tomapel721/Telemetry-Transmitter/Transmitter/SourceCode/Core/Src/NRF24/nRF24.c

/*
 * nRF24.c
 *
 *  Created on: Apr 26, 2020
 *      Author: Mateusz Salamon
 */

#include "main.h"
#include "spi.h"

#include "nRF24/nRF24.h"
#include "nRF24/nRF24_Defs.h"
#include "NRF24/ring_buffer.h"


static SPI_HandleTypeDef *hspi_nrf;

static uint8_t addr_p0_backup[NRF24_ADDR_SIZE];

#if (NRF24_USE_INTERRUPT == 1)
static uint8_t nrf24_rx_flag, nrf24_tx_flag, nrf24_mr_flag;
static volatile uint8_t Nrf24InterruptFlag, Nrf24RXReadyDataFlag;
#endif

#if (NRF24_USE_INTERRUPT == 1)
#if (NRF24_USE_RINGBUFFER == 1)
static uint8_t Nrf24TXFreeFlag;
static RingBuffer *RXBuffer, *TXBuffer;
#endif
#if (NRF24_USE_RINGBUFFER == 0)
static uint8_t RXBuffer[32];
static uint8_t RXDataCounter;
#endif
#endif

//
// BASIC READ/WRITE FUNCTIONS
//
// Define these function for your MCU
//

#define NRF24_CSN_HIGH		HAL_GPIO_WritePin(NRF24_CSN_GPIO_Port, NRF24_CSN_Pin, GPIO_PIN_SET)
#define NRF24_CSN_LOW		HAL_GPIO_WritePin(NRF24_CSN_GPIO_Port, NRF24_CSN_Pin, GPIO_PIN_RESET)

#define NRF24_CE_HIGH		HAL_GPIO_WritePin(NRF24_CE_GPIO_Port, NRF24_CE_Pin, GPIO_PIN_SET)
#define NRF24_CE_LOW		HAL_GPIO_WritePin(NRF24_CE_GPIO_Port, NRF24_CE_Pin, GPIO_PIN_RESET)

static void nRF24_Delay_ms(uint8_t Time)
{
	HAL_Delay(Time);
}

static void nRF24_SendSpi(uint8_t *Data, uint8_t Length)
{
	HAL_SPI_Transmit(hspi_nrf, Data, Length, 1000);
}

static void nRF24_ReadSpi(uint8_t *Data, uint8_t Length)
{
	HAL_SPI_Receive(hspi_nrf, Data, Length, 1000);
}

//
// END OF BASIC READ/WRITE FUNCTIONS
//
static uint8_t nRF24_ReadRegister(uint8_t reg)
{
	uint8_t result;

	reg = NRF24_CMD_R_REGISTER | reg;

	NRF24_CSN_LOW;
	nRF24_SendSpi(&reg, 1);
	nRF24_ReadSpi(&result, 1);
	NRF24_CSN_HIGH;

	return result;
}

static void nRF24_ReadRegisters(uint8_t reg, uint8_t* ret, uint8_t len)
{
	reg = NRF24_CMD_R_REGISTER | reg;

	NRF24_CSN_LOW;

	nRF24_SendSpi(&reg, 1);
	nRF24_ReadSpi(ret, len);

	NRF24_CSN_HIGH;
}

static void nRF24_WriteRegister(uint8_t reg, uint8_t val)
{
	uint8_t tmp[2];

	tmp[0] = NRF24_CMD_W_REGISTER | reg;
	tmp[1] = val;

	NRF24_CSN_LOW;

	nRF24_SendSpi(tmp, 2);

	NRF24_CSN_HIGH;
}

static void nRF24_WriteRegisters(uint8_t reg, uint8_t* val, uint8_t len)
{
	reg = NRF24_CMD_W_REGISTER | reg;

	NRF24_CSN_LOW;

	nRF24_SendSpi(&reg, 1);
	nRF24_SendSpi(val, len);

	NRF24_CSN_HIGH;
}

void nRF24_RX_Mode(void)
{
	uint8_t config = nRF24_ReadConfig();
	// Restore pipe 0 adress after comeback from TX mode
	nRF24_SetRXAddress(0, addr_p0_backup);
	// PWR_UP bit set
	config |= (1<<NRF24_PWR_UP);
	// PRIM_RX bit set
	config |= (1<<NRF24_PRIM_RX);
	nRF24_WriteConfig(config);
	// Reset status
	nRF24_WriteStatus((1<<NRF24_RX_DR)|(1<<NRF24_TX_DS)|(1<<NRF24_MAX_RT));
	// Flush RX
	nRF24_FlushRX();
	// Flush TX
	nRF24_FlushTX();

	NRF24_CE_HIGH;
	nRF24_Delay_ms(1);
}

void nRF24_TX_Mode(void)
{
	NRF24_CE_LOW;

	uint8_t config = nRF24_ReadConfig();
	// PWR_UP bit set
	config |= (1<<NRF24_PWR_UP);
	// PRIM_RX bit low
	config &= ~(1<<NRF24_PRIM_RX);
	nRF24_WriteConfig(config);
	// Reset status
	nRF24_WriteStatus((1<<NRF24_RX_DR)|(1<<NRF24_TX_DS)|(1<<NRF24_MAX_RT));
	// Flush RX
	nRF24_FlushRX();
	// Flush TX
	nRF24_FlushTX();

	nRF24_Delay_ms(1);
}

uint8_t nRF24_ReadConfig(void)
{
	return (nRF24_ReadRegister(NRF24_CONFIG));
}

void nRF24_WriteConfig(uint8_t conf)
{
	nRF24_WriteRegister(NRF24_CONFIG, conf);
}

void nRF24_SetPALevel(uint8_t lev)
{
	uint8_t rf_setup = nRF24_ReadRegister(NRF24_RF_SETUP);
	rf_setup &= 0xF8; // Clear PWR bits
	rf_setup |= (lev<<1);
	nRF24_WriteRegister(NRF24_RF_SETUP, rf_setup);
}

void nRF24_SetDataRate(uint8_t dr)
{
	uint8_t rf_setup = nRF24_ReadRegister(NRF24_RF_SETUP);
	rf_setup &= 0xD7; // Clear DR bits (1MBPS)
	if(dr == NRF24_RF_DR_250KBPS)
		rf_setup |= (1<<NRF24_RF_DR_LOW);
	else if(dr == NRF24_RF_DR_2MBPS)
		rf_setup |= (1<<NRF24_RF_DR_HIGH);
	nRF24_WriteRegister(NRF24_RF_SETUP, rf_setup);
}

uint8_t nRF24_ReadStatus(void)
{
	return (nRF24_ReadRegister(NRF24_STATUS));
}

void nRF24_WriteStatus(uint8_t st)
{
	nRF24_WriteRegister(NRF24_STATUS, st);
}

//
// FIFO Status
//

uint8_t nRF24_ReadFifoStatus(void)
{
	return (nRF24_ReadRegister(NRF24_FIFO_STATUS));
}

void nRF24_WriteFifoStatus(uint8_t st)
{
	nRF24_WriteRegister(NRF24_FIFO_STATUS, st);
}

uint8_t nRF24_IsBitSetInFifoStatus(uint8_t Bit)
{
	uint8_t FifoStatus;

	FifoStatus = nRF24_ReadFifoStatus();

	if(FifoStatus & (1<<Bit))
	{
		return 1;
	}

	return 0;
}

uint8_t nRF24_IsTxReuse(void)
{
	return nRF24_IsBitSetInFifoStatus(NRF24_TX_REUSE);
}

uint8_t nRF24_IsTxFull(void)
{
	return nRF24_IsBitSetInFifoStatus(NRF24_TX_FULL);
}

uint8_t nRF24_IsTxEmpty(void)
{
	return nRF24_IsBitSetInFifoStatus(NRF24_TX_EMPTY);
}

uint8_t nRF24_IsRxFull(void)
{
	return nRF24_IsBitSetInFifoStatus(NRF24_RX_FULL);
}

uint8_t nRF24_IsRxEmpty(void)
{
	return nRF24_IsBitSetInFifoStatus(NRF24_RX_EMPTY);
}

void nRF24_FlushRX(void)
{
	uint8_t command = NRF24_CMD_FLUSH_RX;

	NRF24_CSN_LOW;
	nRF24_SendSpi(&command, 1);
	NRF24_CSN_HIGH;
}

void nRF24_FlushTX(void)
{
	uint8_t command = NRF24_CMD_FLUSH_TX;

	NRF24_CSN_LOW;
	nRF24_SendSpi(&command, 1);
	NRF24_CSN_HIGH;
}

void nRF24_EnableCRC(uint8_t onoff)
{
	uint8_t config = nRF24_ReadConfig();

	if(onoff)
		config |= (1<<NRF24_EN_CRC);
	else
		config &= ~(1<<NRF24_EN_CRC);
	nRF24_WriteConfig(config);
}

void nRF24_SetCRCLength(uint8_t crcl)
{
	uint8_t config = nRF24_ReadConfig();
	if(crcl == NRF24_CRC_WIDTH_2B)
		config |= (1<<NRF24_CRCO);
	else
		config &= ~(1<<NRF24_CRCO);
	nRF24_WriteConfig(config);
}

void nRF24_SetRetries(uint8_t ard, uint8_t arc)
{
	// ard * 250us, arc repeats
	nRF24_WriteRegister(NRF24_SETUP_RETR, (((ard & 0x0F)<<NRF24_ARD) | ((arc & 0x0F)<<NRF24_ARC)));
}

void nRF24_SetRFChannel(uint8_t channel)
{
	nRF24_WriteRegister(NRF24_RF_CH, (channel & 0x7F));
}

void nRF24_SetPayloadSize(uint8_t pipe, uint8_t size)
{
	if(pipe > 5)
		pipe = 5; // Block too high pipe number
	nRF24_WriteRegister(NRF24_RX_PW_P0 + pipe , (size & 0x3F));
}

void nRF24_EnablePipe(uint8_t pipe, uint8_t onoff)
{
	if(pipe > 5)
		pipe = 5; // Block too high pipe number
	uint8_t enable_pipe = nRF24_ReadRegister(NRF24_EN_RXADDR);
	if(onoff == 1)
		enable_pipe |= (1<<pipe);
	else
		enable_pipe &= ~(1<<pipe);
	nRF24_WriteRegister(NRF24_EN_RXADDR, enable_pipe);
}

void nRF24_AutoACK(uint8_t pipe, uint8_t onoff)
{
	if(pipe > 5)
		pipe = 5; // Block too high pipe number
	uint8_t enaa = nRF24_ReadRegister(NRF24_EN_AA);
	if(onoff == 1)
		enaa |= (1<<pipe);
	else
		enaa &= ~(1<<pipe);
	nRF24_WriteRegister(NRF24_EN_AA, enaa);
}

void nRF24_SetAddressWidth(uint8_t size)
{
	if(size > 5)
		size = 5; // Maximum are 5 bytes
	if(size < 3)
		size = 3; // Minimum are 3 bytes
	nRF24_WriteRegister(NRF24_SETUP_AW, ((size-2) & 0x03));
}

void nRF24_SetRXAddress(uint8_t pipe, const uint8_t* address)
{
	// pipe 0 and pipe 1 are fully 40-bits storaged
	// pipe 2-5 is storaged only with last byte. Rest are as same as pipe 1
	// pipe 0 and 1 are LSByte first so they are needed to reverse address
	if((pipe == 0) || (pipe == 1))
	{
		uint8_t i;
		uint8_t address_rev[NRF24_ADDR_SIZE];
		for(i = 0; i<NRF24_ADDR_SIZE; i++)
			address_rev[NRF24_ADDR_SIZE - 1 - i] = address[i];
		nRF24_WriteRegisters(NRF24_RX_ADDR_P0 + pipe, address_rev, NRF24_ADDR_SIZE);
	}
	else
		nRF24_WriteRegister(NRF24_RX_ADDR_P0 + pipe, address[NRF24_ADDR_SIZE-1]);
}

void nRF24_SetTXAddress(const uint8_t* address)
{
	// TX address is storaged similar to RX pipe 0 - LSByte first
	uint8_t i;
	uint8_t address_rev[NRF24_ADDR_SIZE];

	nRF24_ReadRegisters(NRF24_RX_ADDR_P0, address_rev, NRF24_ADDR_SIZE); // Backup P0 address
	for(i = 0; i<NRF24_ADDR_SIZE; i++)
		addr_p0_backup[NRF24_ADDR_SIZE - 1 - i] = address_rev[i]; //Reverse P0 address

	for(i = 0; i<NRF24_ADDR_SIZE; i++)
		address_rev[NRF24_ADDR_SIZE - 1 - i] = address[i];
	//make pipe 0 address backup;

	nRF24_WriteRegisters(NRF24_RX_ADDR_P0, address_rev, NRF24_ADDR_SIZE); // Pipe 0 must be same for auto ACk
	nRF24_WriteRegisters(NRF24_TX_ADDR, address_rev, NRF24_ADDR_SIZE);
}

void nRF24_ClearInterrupts(void)
{
	uint8_t status = nRF24_ReadStatus();
	status |= (7<<4); // Clear bits 4, 5, 6.
	nRF24_WriteStatus(status);
}

uint8_t nRF24_GetDynamicPayloadSize(void)
{
    uint8_t result = 0;

    result = nRF24_ReadRegister(NRF24_CMD_R_RX_PL_WID);

    if (result > 32) // Something went wrong :)
    {
        nRF24_FlushRX();
        nRF24_Delay_ms(2);
        return 0;
    }
    return result;
}

void nRF24_EnableRXDataReadyIRQ(uint8_t onoff)
{
	uint8_t config = nRF24_ReadConfig();

	if(!onoff)
		config |= (1<<NRF24_RX_DR);
	else
		config &= ~(1<<NRF24_RX_DR);

	nRF24_WriteConfig(config);
}

void nRF24_EnableTXDataSentIRQ(uint8_t onoff)
{
	uint8_t config = nRF24_ReadConfig();

	if(!onoff)
		config |= (1<<NRF24_TX_DS);
	else
		config &= ~(1<<NRF24_TX_DS);

	nRF24_WriteConfig(config);
}

void nRF24_EnableMaxRetransmitIRQ(uint8_t onoff)
{
	uint8_t config = nRF24_ReadConfig();

	if(!onoff)
		config |= (1<<NRF24_MAX_RT);
	else
		config &= ~(1<<NRF24_MAX_RT);

	nRF24_WriteConfig(config);
}

void nRF24_WriteTXPayload(uint8_t * data, __attribute__((unused))uint8_t size)
{
#if (NRF24_DYNAMIC_PAYLOAD == 1)
	nRF24_WriteRegisters(NRF24_CMD_W_TX_PAYLOAD, data, size);
#else
	nRF24_WriteRegisters(NRF24_CMD_W_TX_PAYLOAD, data, NRF24_PAYLOAD_SIZE);
#endif
}

void nRF24_WaitTX()
{
	uint8_t status;
	NRF24_CE_HIGH;
	nRF24_Delay_ms(1);
	NRF24_CE_LOW;
	do
	{
		nRF24_Delay_ms(1);
		status = nRF24_ReadStatus();
	}while(!((status & (1<<NRF24_MAX_RT)) || (status & (1<<NRF24_TX_DS))));
}

void nRF24_ReadRXPaylaod(uint8_t *data, __attribute__((unused))uint8_t *size)
{
#if (NRF24_DYNAMIC_PAYLOAD == 1)
	*size = nRF24_GetDynamicPayloadSize();
	nRF24_ReadRegisters(NRF24_CMD_R_RX_PAYLOAD, data, *size);
#else
	nRF24_ReadRegisters(NRF24_CMD_R_RX_PAYLOAD, data, NRF24_PAYLOAD_SIZE);
#endif
#if (NRF24_INTERRUPT_MODE == 0)
	nRF24_WriteRegister(NRF24_STATUS, (1<NRF24_RX_DR));
	if(nRF24_ReadStatus() & (1<<NRF24_TX_DS))
		nRF24_WriteRegister(NRF24_STATUS, (1<<NRF24_TX_DS));
#endif
}

nRF24_TX_Status nRF24_SendPacket(uint8_t* Data, uint8_t Size)
{
	if(Size > 32)
		return NRF24_NO_TRANSMITTED_PACKET;

	nRF24_WriteTXPayload(Data, Size);
#if (NRF24_USE_RINGBUFFER == 0)
	nRF24_WaitTX();
#endif


	return NRF24_TRANSMITTED_PACKET;
}

#if (NRF24_USE_RINGBUFFER == 1)
uint8_t nRF24_IsSomtehingToRead(void)
{
	return RB_ElementsAvailable(RXBuffer)?1:0;
}

uint8_t nRF24_IsSomtehingToSend(void)
{
	return RB_ElementsAvailable(TXBuffer)?1:0;
}
#endif

uint8_t nRF24_RXAvailable(void)
{
#if (NRF24_USE_INTERRUPT == 0)
	uint8_t status = nRF24_ReadStatus();

	// RX FIFO Interrupt
	if ((status & (1 << 6)))
	{
		status |= (1<<6); // Interrupt flag clear
		nRF24_WriteStatus(status);
		return 1;
	}
	return 0;
#endif
#if (NRF24_USE_INTERRUPT == 1) && (NRF24_USE_RINGBUFFER == 0)
	if(RXDataCounter > 0)
	{
		return 1;
	}
	return 0;
#endif
#if (NRF24_USE_RINGBUFFER == 1)
	return nRF24_IsSomtehingToRead();
#endif
}

nRF24_RX_Status nRF24_ReceivePacket(uint8_t* Data, uint8_t *Size)
{
#if (NRF24_USE_INTERRUPT == 0)
	if(nRF24_RXAvailable())
	{
#endif
		nRF24_ReadRXPaylaod(Data, Size);
		return NRF24_RECEIVED_PACKET;
#if (NRF24_USE_INTERRUPT == 0)
	}
	return NRF24_NO_RECEIVED_PACKET;
#endif

}

nRF24_TX_Status nRF24_SendData(uint8_t* Data, uint8_t Size)
{
static int licznikRamek = 0;
#if (NRF24_USE_RINGBUFFER != 1) // (NRF24_USE_INTERRUPT any)
	return nRF24_SendPacket(Data, Size);
#endif
#if (NRF24_USE_RINGBUFFER == 1)
	uint8_t i = 0;

	while(Size > 0)
	{
		if(RB_OK == RB_WriteToBuffer(TXBuffer, Data[i++]))
		{
			Size--;
		}
		else
		{
			return NRF24_NO_TRANSMITTED_PACKET;
		}
	}
	licznikRamek++;
	return NRF24_TRANSMITTED_PACKET;
#endif
}
#if (NRF24_USE_RINGBUFFER == 1)
void nRF24_CheckTXAndSend(void)
{
	uint8_t i, DataCounter;
	uint8_t TXPacket[32];

	if(nRF24_IsSomtehingToSend() && Nrf24TXFreeFlag)
	{
		nRF24_TX_Mode();

		Nrf24TXFreeFlag = 0;
		DataCounter = RB_ElementsAvailable(TXBuffer);
		if(DataCounter > 32)
		{
			DataCounter = 32; // Max Payload
		}

		for(i = 0; i < DataCounter; i++)
		{
			RB_ReadFromBuffer(TXBuffer, &TXPacket[i]);
		}

		nRF24_SendPacket(TXPacket, DataCounter);
		NRF24_CE_HIGH;
		nRF24_Delay_ms(1);
		NRF24_CE_LOW;
	}
}
#endif
#if (NRF24_USE_INTERRUPT == 1)
void nRF24_ReceiveData(void)
{
#if (NRF24_USE_RINGBUFFER == 1)
	uint8_t i, DataCounter;
	uint8_t RXPacket[32];
	do
	{
		nRF24_ReceivePacket(RXPacket, &DataCounter);

		for(i = 0; i < DataCounter; i++)
		{
			RB_WriteToBuffer(RXBuffer, RXPacket[i]);
		}

	}while(!nRF24_IsRxEmpty());
#endif
#if (NRF24_USE_RINGBUFFER == 0)
	nRF24_ReceivePacket(RXBuffer, &RXDataCounter);
#endif
}
#endif

nRF24_RX_Status nRF24_ReadData(uint8_t *Data, uint8_t *Size)
{
#if (NRF24_USE_INTERRUPT == 0)
	if(NRF24_RECEIVED_PACKET == nRF24_ReceivePacket(Data, Size))
	{
		return NRF24_RECEIVED_PACKET;
	}
	*Size = 0;
	return NRF24_NO_RECEIVED_PACKET;
#endif
#if (NRF24_USE_INTERRUPT == 1)
	uint8_t i = 0;
	*Size = 0;

	  if(nRF24_RXAvailable())
	  {
#if (NRF24_USE_RINGBUFFER == 1)
		while(RB_OK == RB_ReadFromBuffer(RXBuffer, &Data[i]))
		{
			i++;
		}
		*Size = i;
#endif
#if (NRF24_USE_RINGBUFFER == 0)
		for(i = 0; i < RXDataCounter; i++)
		{
			Data[i] = RXBuffer[i];
		}
#endif
	  }
#if (NRF24_USE_RINGBUFFER == 0)
	*Size = RXDataCounter;
	RXDataCounter = 0;
#endif
	if(*Size == 0)
	{
		return NRF24_NO_RECEIVED_PACKET;
	}

	return NRF24_RECEIVED_PACKET;
#endif
}

#if (NRF24_USE_INTERRUPT == 1)
void nRF24_IRQ_Handler(void)
{
	Nrf24InterruptFlag = 1;
}

void nRF24_IRQ_Read(void)
{
	if(Nrf24InterruptFlag == 1)
	{
		Nrf24InterruptFlag = 0;

		uint8_t status = nRF24_ReadStatus();
		uint8_t ClearIrq = 0;
		// RX FIFO Interrupt
		if ((status & (1 << NRF24_RX_DR)))
		{
			nrf24_rx_flag = 1;
			ClearIrq |= (1<<NRF24_RX_DR); // Interrupt flag clear
		}
		// TX Data Sent interrupt
		if ((status & (1 << NRF24_TX_DS)))
		{
			nrf24_tx_flag = 1;
			ClearIrq |= (1<<NRF24_TX_DS); // Interrupt flag clear
		}
		// Max Retransmits interrupt
		if ((status & (1 << NRF24_MAX_RT)))
		{
			nrf24_mr_flag = 1;
			ClearIrq |= (1<<NRF24_MAX_RT); // Interrupt flag clear
		}

		nRF24_WriteStatus(ClearIrq);
	}
}

//
// Additional callbacks for Interrupt mode
//

__weak void nRF24_EventRxCallback(void)
{

}

__weak void nRF24_EventTxCallback(void)
{

}

__weak void nRF24_EventMrCallback(void)
{

}

void nRF24_Event(void)
{
	nRF24_IRQ_Read(); // Check if there was any interrupt

#if (NRF24_USE_RINGBUFFER == 1)
	nRF24_CheckTXAndSend();
#endif

	if(nrf24_rx_flag)
	{
#if (NRF24_USE_INTERRUPT == 1)
		nRF24_ReceiveData();
#endif
		nRF24_EventRxCallback();
		nrf24_rx_flag = 0;
	}

	if(nrf24_tx_flag)
	{
#if (NRF24_USE_RINGBUFFER == 1)
		Nrf24TXFreeFlag = 1;
#endif
		nRF24_EventTxCallback();
		nrf24_tx_flag = 0;
	}

	if(nrf24_mr_flag)
	{
		nRF24_EventMrCallback();
		nrf24_mr_flag = 0;
	}
}
#endif

void nRF24_Init(SPI_HandleTypeDef *hspi)
{
	hspi_nrf = hspi;

	NRF24_CE_LOW;
	NRF24_CSN_HIGH;

	nRF24_Delay_ms(5); // Wait for radio power up

	nRF24_SetPALevel(NRF24_PA_PWR_0dBM); // Radio power
	nRF24_SetDataRate(NRF24_RF_DR_1MBPS); // Data Rate
	nRF24_EnableCRC(1); // Enable CRC
	nRF24_SetCRCLength(NRF24_CRC_WIDTH_1B); // CRC Length 1 byte
	nRF24_SetRetries(0x04, 0x07); // 1000us, 7 times

#if (NRF24_DYNAMIC_PAYLOAD == 1)
	nRF24_WriteRegister(NRF24_FEATURE, nRF24_ReadRegister(NRF24_FEATURE) | (1<<NRF24_EN_DPL)); // Enable dynamic payload feature
	nRF24_WriteRegister(NRF24_DYNPD, 0x3F); // Enable dynamic payloads for all pipes
#else
	nRF24_WriteRegister(NRF24_DYNPD, 0); // Disable dynamic payloads for all pipes
	nRF24_SetPayloadSize(0, NRF24_PAYLOAD_SIZE); // Set 32 bytes payload for pipe 0
#endif
	nRF24_SetRFChannel(10); // Set RF channel for transmission
	nRF24_EnablePipe(0, 1); // Enable pipe 0
	nRF24_AutoACK(0, 1); // Enable auto ACK for pipe 0
	nRF24_SetAddressWidth(NRF24_ADDR_SIZE); // Set address size

	nRF24_Delay_ms(1);

#if (NRF24_USE_INTERRUPT == 1)
	nRF24_EnableRXDataReadyIRQ(1);
#endif
#if (NRF24_USE_INTERRUPT == 0)
	nRF24_EnableRXDataReadyIRQ(0);
#endif
	nRF24_EnableTXDataSentIRQ(1);
	nRF24_EnableMaxRetransmitIRQ(1);

	nRF24_Delay_ms(1);

	nRF24_ClearInterrupts();
#if (NRF24_USE_RINGBUFFER == 1)
	nRF24_EnableRXDataReadyIRQ(1);
	nRF24_EnableTXDataSentIRQ(1);
	Nrf24TXFreeFlag = 1;
	RB_CreateBuffer(&TXBuffer, NRF24_TX_BUFFER_SIZE);
	RB_CreateBuffer(&RXBuffer, NRF24_RX_BUFFER_SIZE);
#endif
}
